lukasznowarkiewicz/iPhone13MiniCoolingCase/images/iPhone_12_mini_heatsink_casing_aluminium_1.png

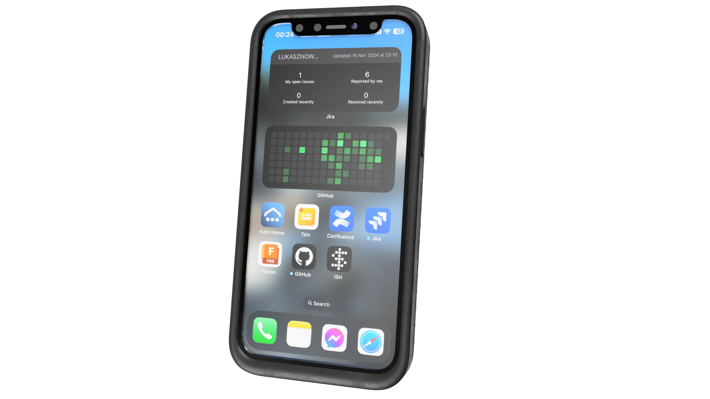
images/iPhone_12_mini_heatsink_casing_aluminium_1.png
