lukasznowarkiewicz/iPhone13MiniCoolingCase/images/iPhone_12_mini_heatsink_casing_aluminium_3.png

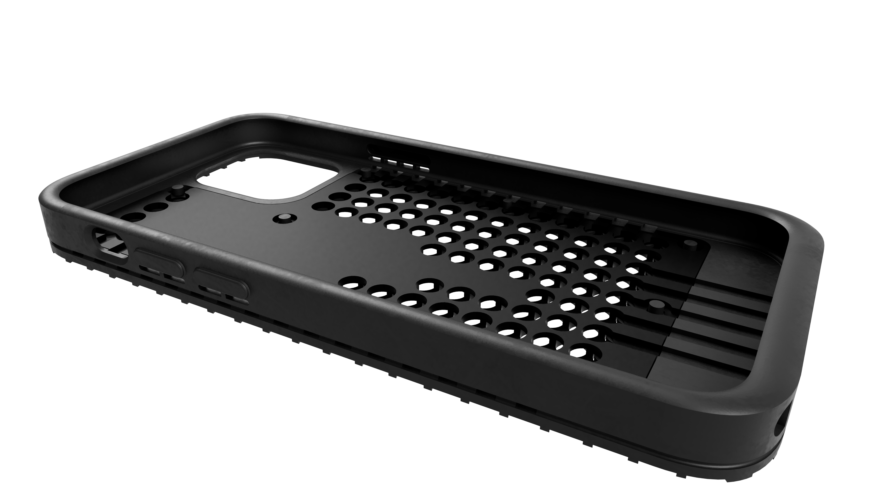
images/iPhone_12_mini_heatsink_casing_aluminium_3.png
