lukasznowarkiewicz/iPhone13MiniCoolingCase/images/iPhone_12_mini_heatsink_casing_copper_1.png

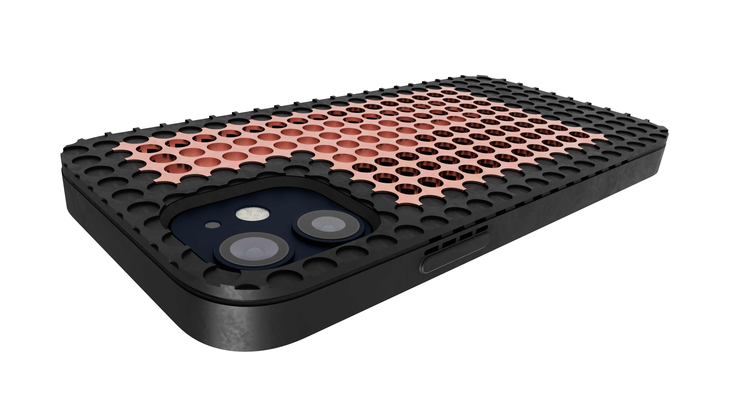
images/iPhone_12_mini_heatsink_casing_copper_1.png
